BUBOYUE/ELEC5550_Design-project/hardware/sim/LaserDriver.asc

C3: cap; 1pF
DOPV300: diode; DOPV300
OPA2350: UniversalOpAmp2; Avol=1Meg GBW=38Meg Slew=22Meg
PR1.1: res; 200
PR1.2: res; 800
Q1: npn; BD139
R1: res; 330E
R2: res; 100K
R3: res; 68
R4: res; 10K
R5: res; 25
R6: res; 10K
R7: res; 100K
V1: voltage; 5V
V2: voltage; PULSE(0 3.3 0 5n 5n 10u 20u)
Named nets: 0
.model DOPV300 D (IS=1e-18 N=1.9 RS=10 Cjo=5p VJ=0.7 M=0.5 TT=1n BV=5 IBV=10u EG=1.42)
.model BD139 NPN(IS=1.25E-14 BF=100 VAF=50 IKF=0.3 ISE=1E-13 NE=1.5 BR=2.5 RC=1 RE=0.5 RB=10 CJE=30E-12 CJC=12E-12 TF=0.35E-9 TR=10E-9 VCEsat=0.5)
.include OPAx350.LIB
.tran 100u
