BUBOYUE/ELEC5550_Design-project/hardware/sim/receiver/receiver.asc

I2: current; PULSE(0u 30u 1.2u 0n 0n 25u 50u 2); AC 1
R1: res; 10K; tol=1 pwr=0.1
R5: res; 10K
R6: res; 10K
R8: res; 10K
R9: res; 1k
U1: LM358
U2: LT1016
U5: OPA855
VCC1: voltage; 5
VCC2: voltage; 3.3
VCC3: voltage; 1
Named nets: 0, VCC, REF, TIA, VDD
.tran 100u
.lib opa855_a.lib
.lib MAX40026.txt
